Etzeban/SmartWateringSystem/J-tube.SLDPRT

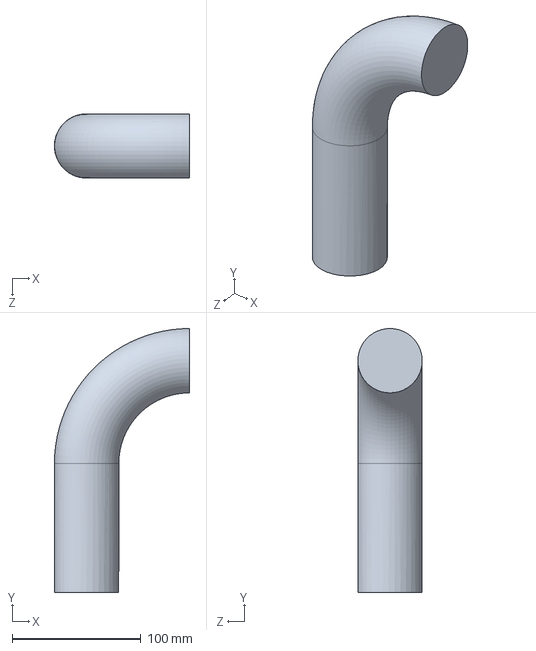
[picture p20: CAD file, 2024-09-25]
J-tube.SLDPRT
105.0 x 205.0 x 49.9 mm
