Etzeban/SmartWateringSystem/Shooting Range.SLDPRT

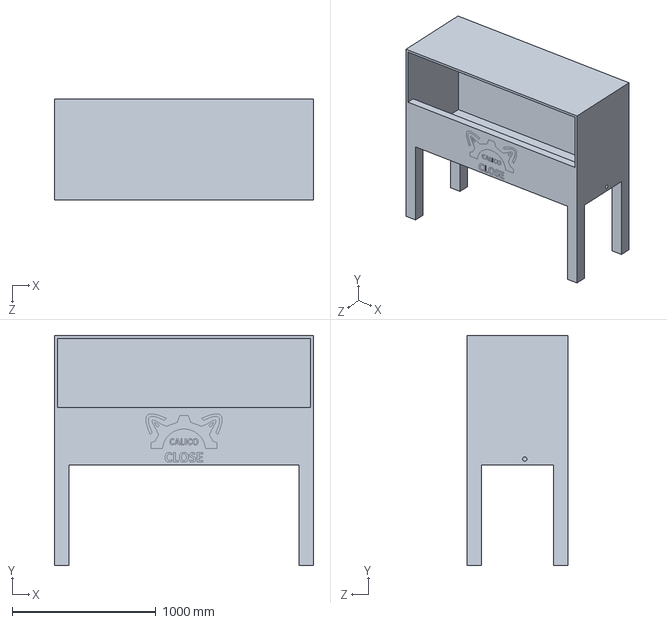
[picture p21: CAD file, 2024-09-25]
Shooting Range.SLDPRT
1800.0 x 1600.0 x 701.0 mm
