Etzeban/SmartWateringSystem/Tube.SLDPRT

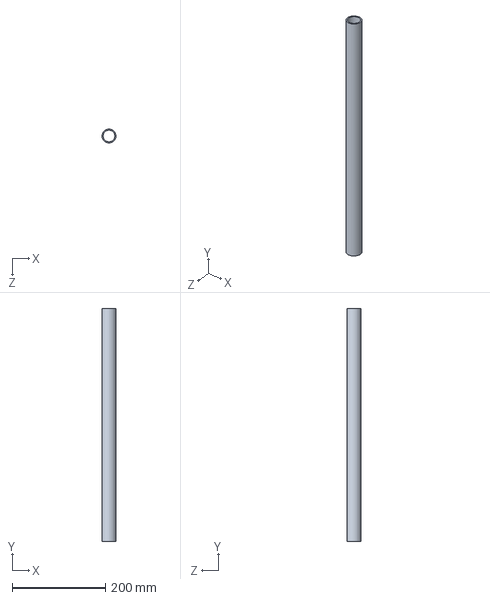
[picture p22: CAD file, 2024-09-25]
Tube.SLDPRT
30.0 x 500.0 x 30.0 mm
