Etzeban/SmartWateringSystem/20L WATER TANK.SLDPRT

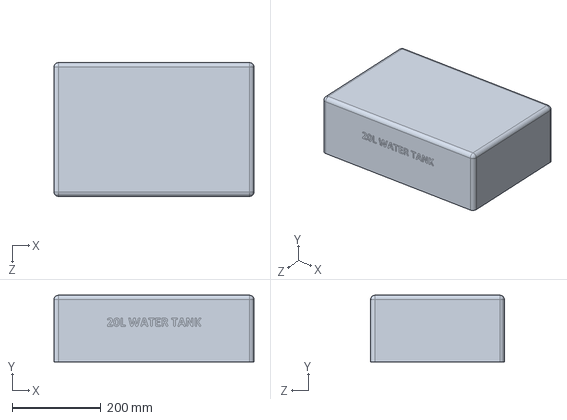
[picture p23: CAD file, 2024-09-25]
20L WATER TANK.SLDPRT
450.0 x 150.0 x 301.0 mm
