Etzeban/SmartWateringSystem/Steel Frame.SLDPRT

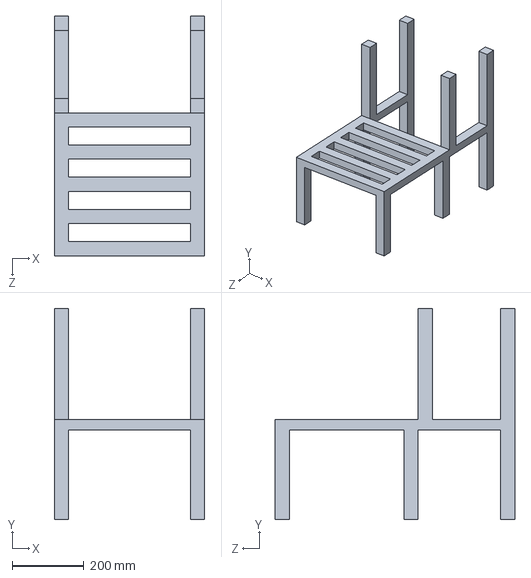
[picture p24: CAD file, 2024-09-25]
Steel Frame.SLDPRT
420.0 x 590.0 x 670.0 mm
