Etzeban/SmartWateringSystem/L-TUBE.SLDPRT

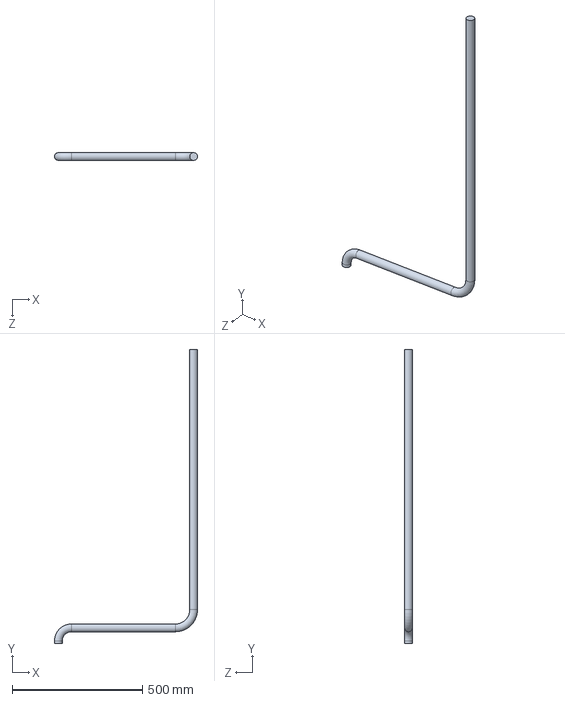
[picture p25: CAD file, 2024-09-25]
L-TUBE.SLDPRT
550.0 x 1130.0 x 30.0 mm
