Etzeban/SmartWateringSystem/Counterweight.SLDPRT

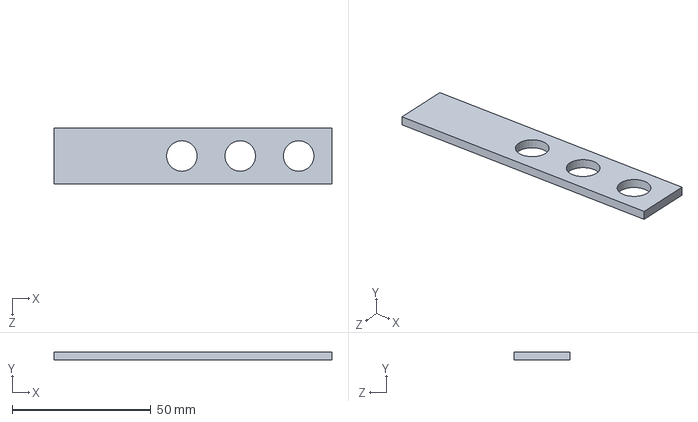
[picture p26: CAD file, 2024-09-24]
Counterweight.SLDPRT
100.0 x 3.00 x 20.0 mm
