Etzeban/SmartWateringSystem/Targets design.SLDPRT

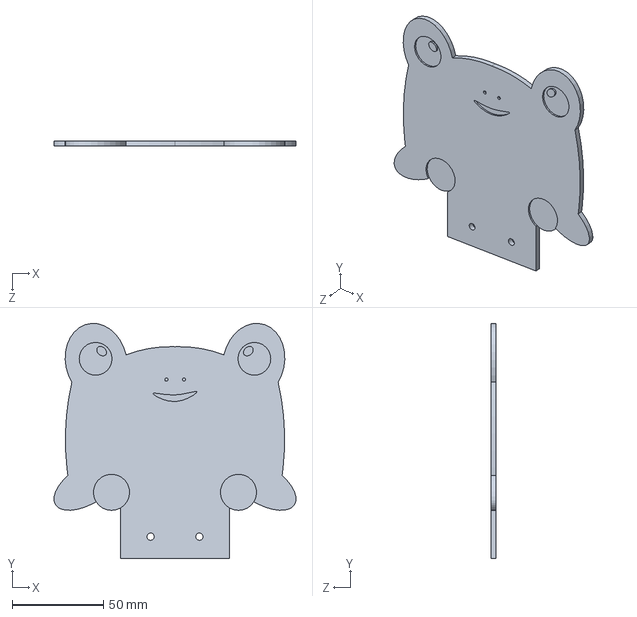
[picture p27: CAD file, 2024-09-24]
Targets design.SLDPRT
132.7 x 128.9 x 3.00 mm
