Etzeban/SmartWateringSystem/Targets Assembled with Counterweight.SLDASM

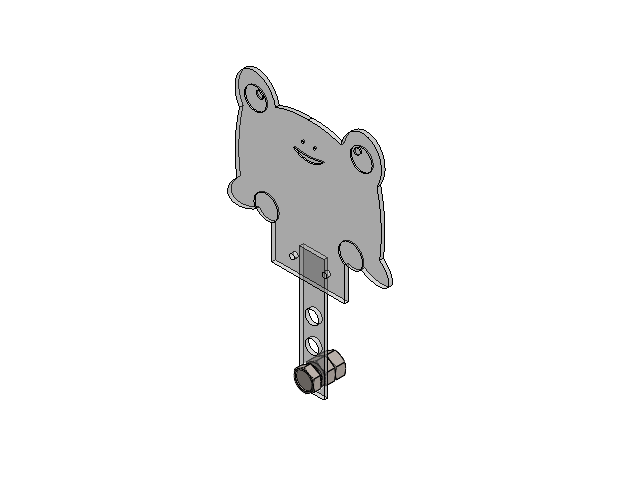
[picture p28: CAD file, 2024-09-24]
Targets Assembled with Counterweight.SLDASM
Targets design
Counterweight
formed hex screw_am
hex nut style 1_am x 2
